WilliamPrime/Kb00-Cursed10/IMGS/RENDERS/aqua plate early.png

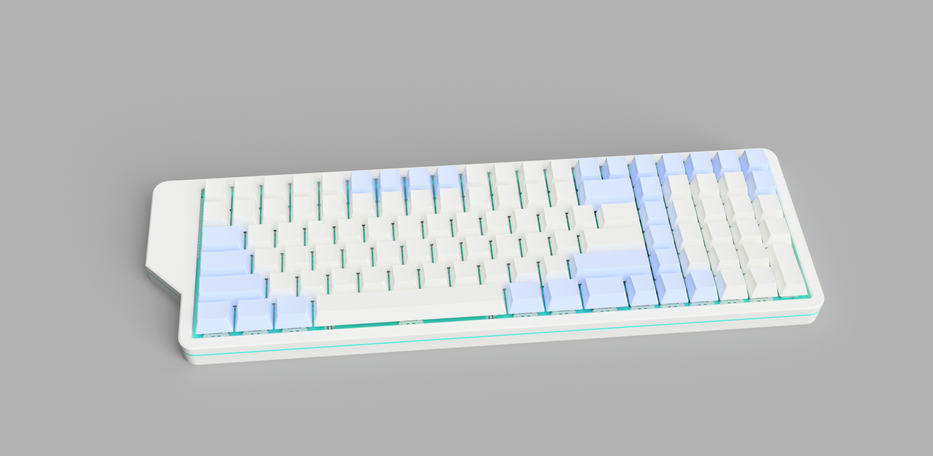
IMGS/RENDERS/aqua plate early.png
